Maker-Melissa/X10Controller/X10FireCracker.h

/* Arduino interface to the CM17A Wireless X10 'Firecracker' dongle. 
  Originally created by BroHogan 7/19/08
  Melissa LeBlanc-Williams Sept 2018
 */

#ifndef X10FireCracker_h
#define X10FireCracker_h
#include <stdint.h>

enum HouseCode { hcA, hcB, hcC, hcD, hcE, hcF, hcG, hcH, 
         hcI, hcJ, hcK, hcL, hcM, hcN, hcO, hcP };

enum CommandCode { cmdOn, cmdOff, cmdBright, cmdDim,
                   cmdAllOff, cmdAllOn, cmdLampsOff, cmdLampsOn };

class X10FireCracker {
public: 
  int RTS_pin;    // RTS line for C17A - DB9 pin 7
  int DTR_pin;    // DTR line for C17A - DB9 pin 4
  int Bit_delay;  // mS delay between bits (0.5mS min.)

  X10FireCracker();
  
  void init( int RTS_Pin, int DTR_Pin, int Bit_Delay );
  void sendCmd(HouseCode house, int device, CommandCode cmnd);
};

extern X10FireCracker X10;

#endif
